noahg460505/Needlessly-Overcomplicated-Widget-Sorter/Diagrams/12_5-Fritzing.png

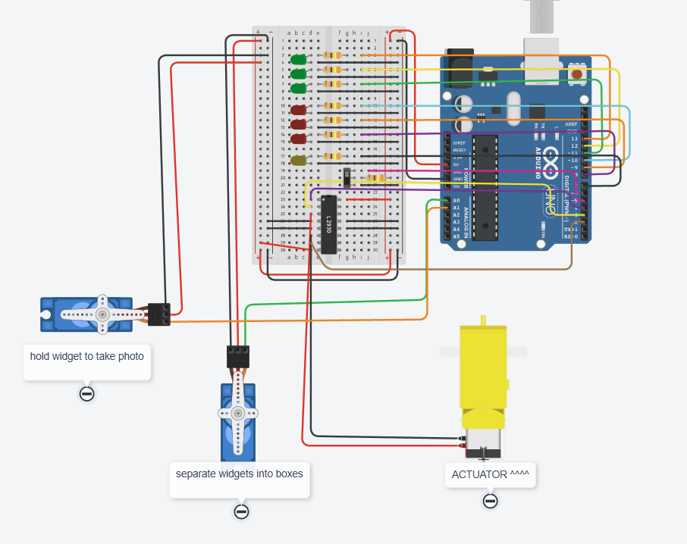
Diagrams/12_5-Fritzing.png
