noahg460505/Needlessly-Overcomplicated-Widget-Sorter/photos-videos/actuator_1.jpg

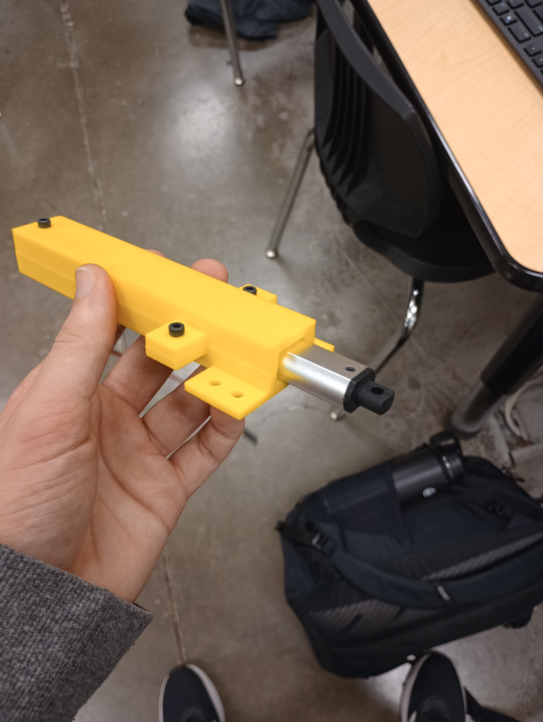
photos-videos/actuator_1.jpg
