noahg460505/Needlessly-Overcomplicated-Widget-Sorter/photos-videos/actuator_2.jpg

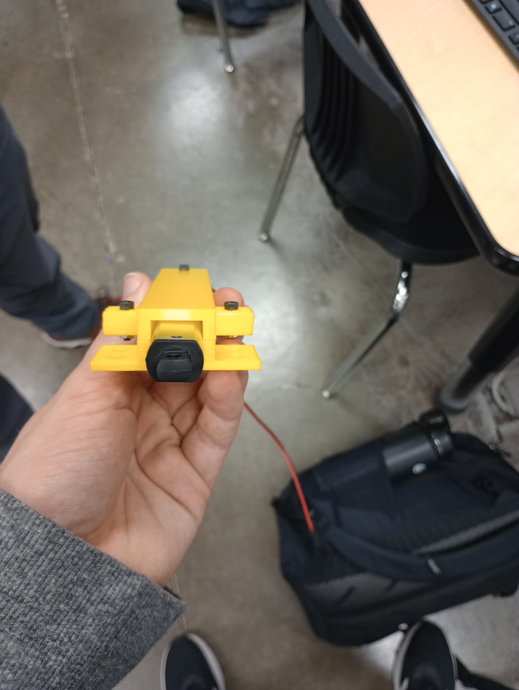
photos-videos/actuator_2.jpg
