noahg460505/Needlessly-Overcomplicated-Widget-Sorter/photos-videos/capture_zone.jpg

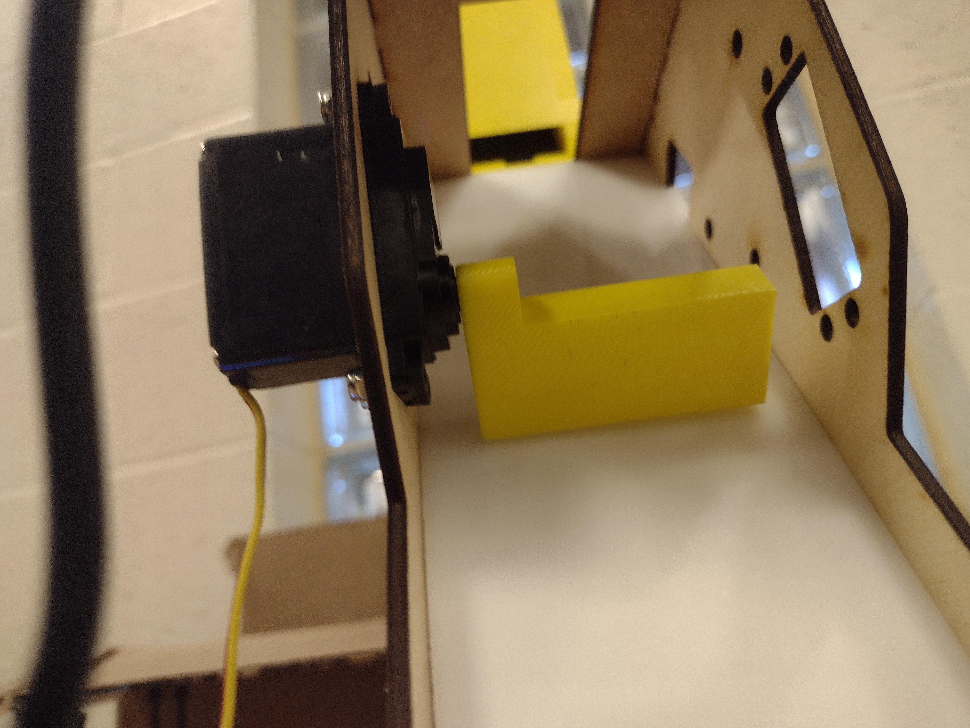
photos-videos/capture_zone.jpg
