noahg460505/Needlessly-Overcomplicated-Widget-Sorter/photos-videos/markus_doing_cad.jpg

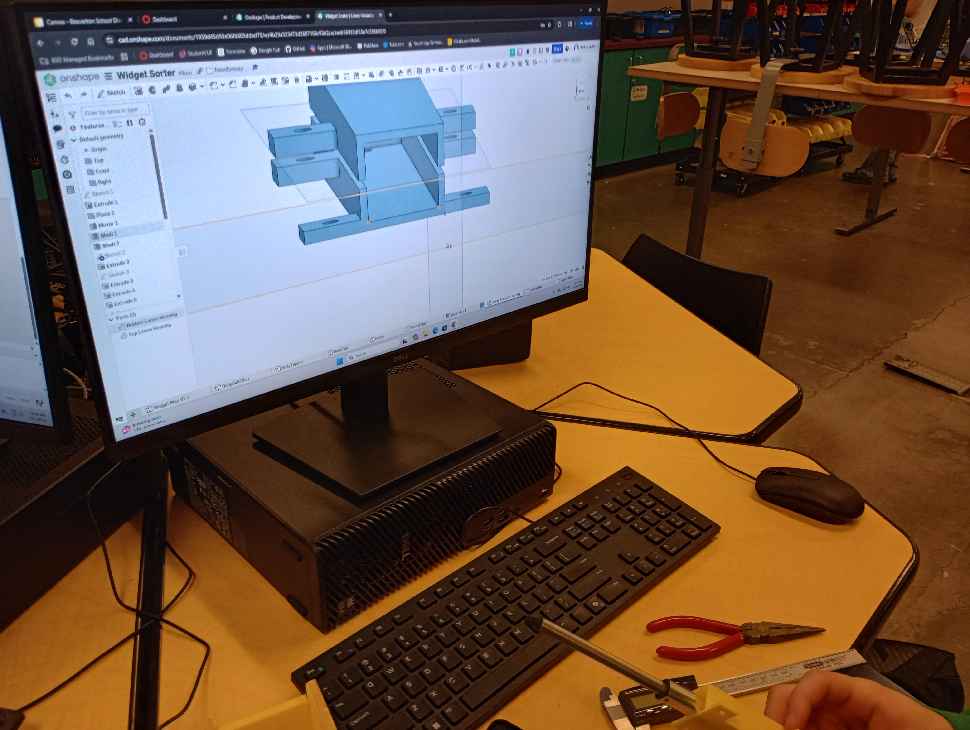
photos-videos/markus_doing_cad.jpg
