noahg460505/Needlessly-Overcomplicated-Widget-Sorter/photos-videos/markus_with_actuator.jpg

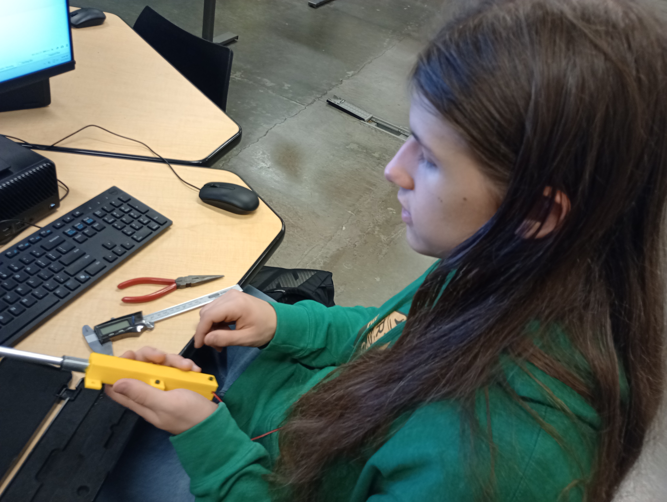
photos-videos/markus_with_actuator.jpg
