noahg460505/Needlessly-Overcomplicated-Widget-Sorter/photos-videos/noah.jpg

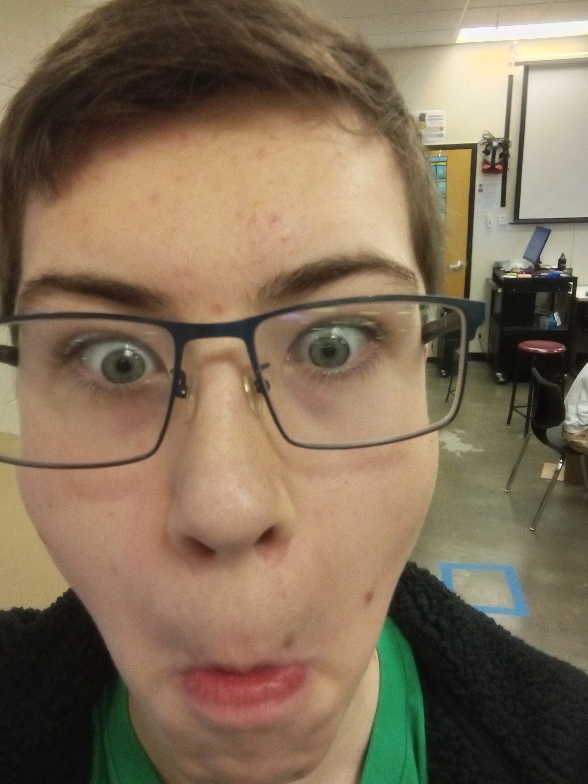
photos-videos/noah.jpg
