noahg460505/Needlessly-Overcomplicated-Widget-Sorter/photos-videos/servo_motor.jpg

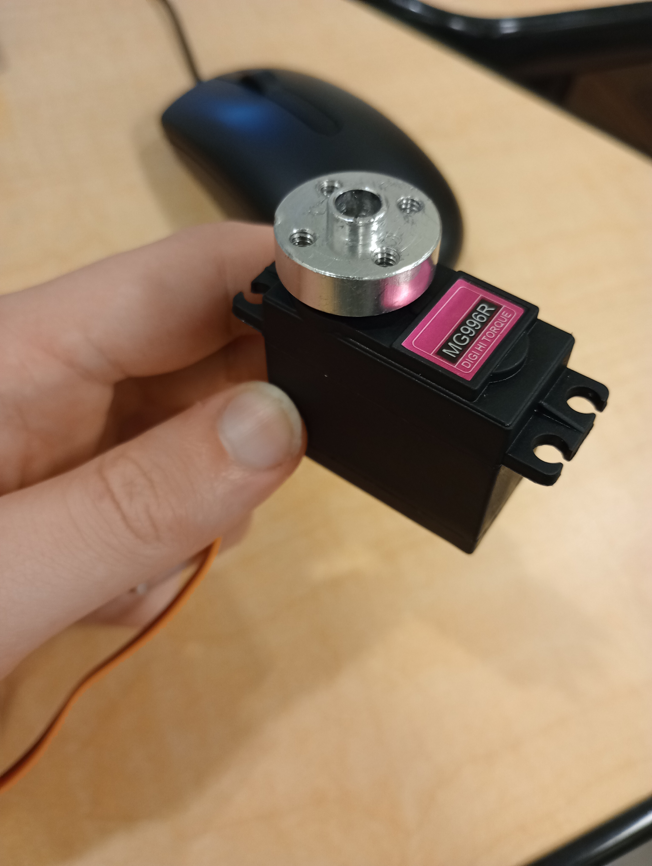
photos-videos/servo_motor.jpg
