noahg460505/Needlessly-Overcomplicated-Widget-Sorter/photos-videos/widget_mag_1.jpg

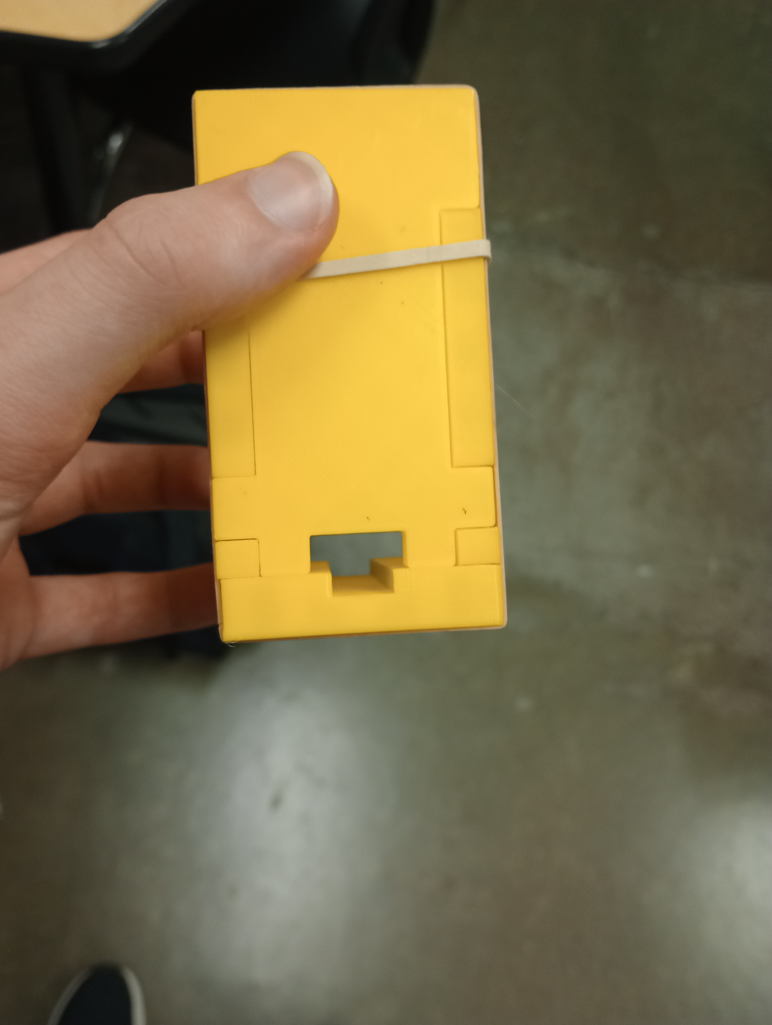
photos-videos/widget_mag_1.jpg
