noahg460505/Needlessly-Overcomplicated-Widget-Sorter/photos-videos/yarema.jpg

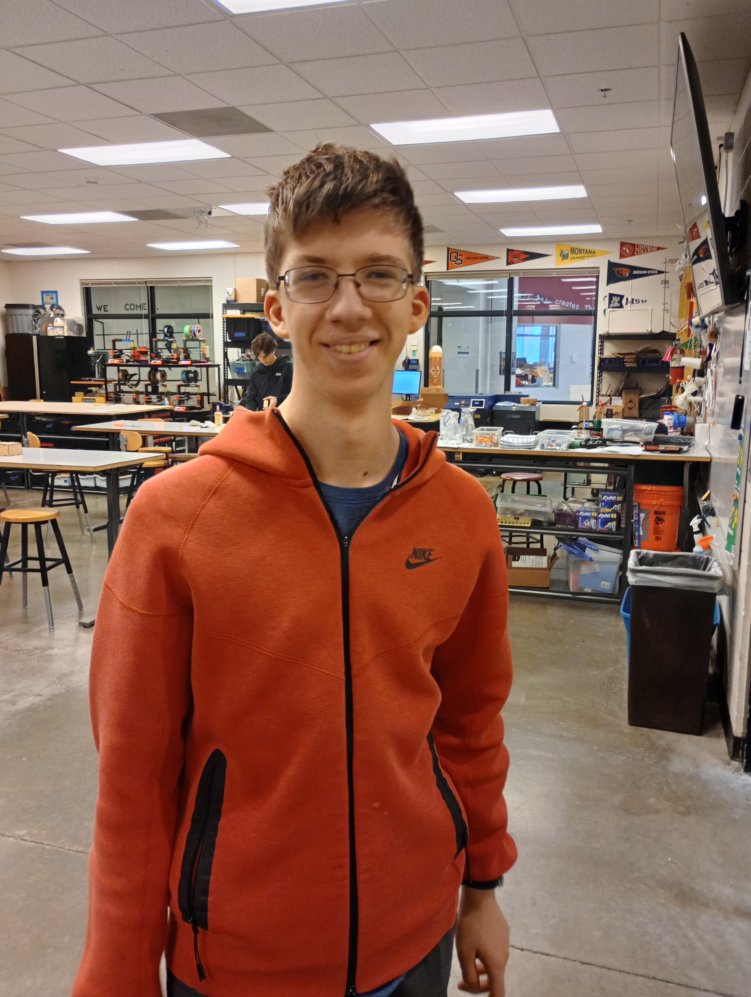
photos-videos/yarema.jpg
