noahg460505/Needlessly-Overcomplicated-Widget-Sorter/CAD/laser-files/flipper-flopper.dxf

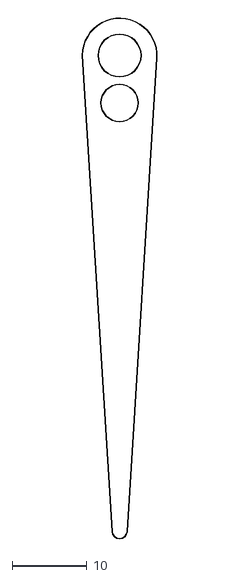
[picture p45: CAD file, 2026-01-20]
CAD/laser-files/flipper-flopper.dxf
10.1 x 70.1
