noahg460505/Needlessly-Overcomplicated-Widget-Sorter/Diagrams/12_1-Wiring.png

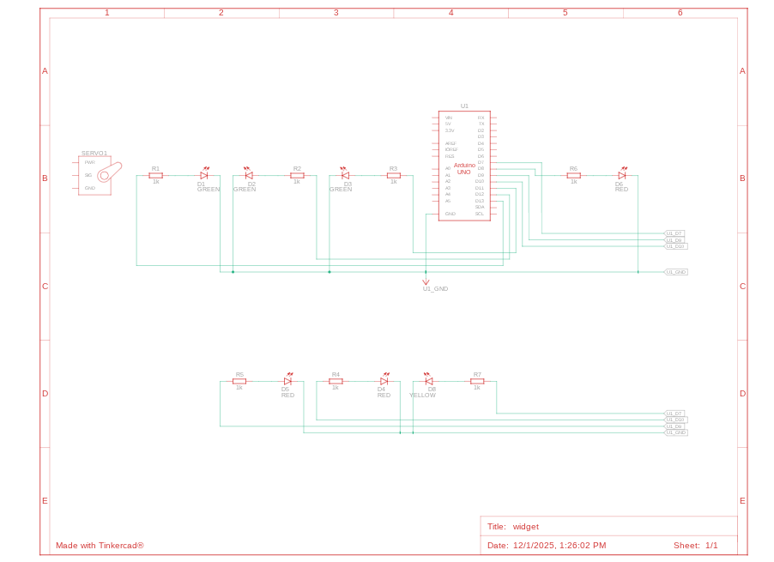
Diagrams/12_1-Wiring.png
