noahg460505/Needlessly-Overcomplicated-Widget-Sorter/Diagrams/12_3 - Wiring.png

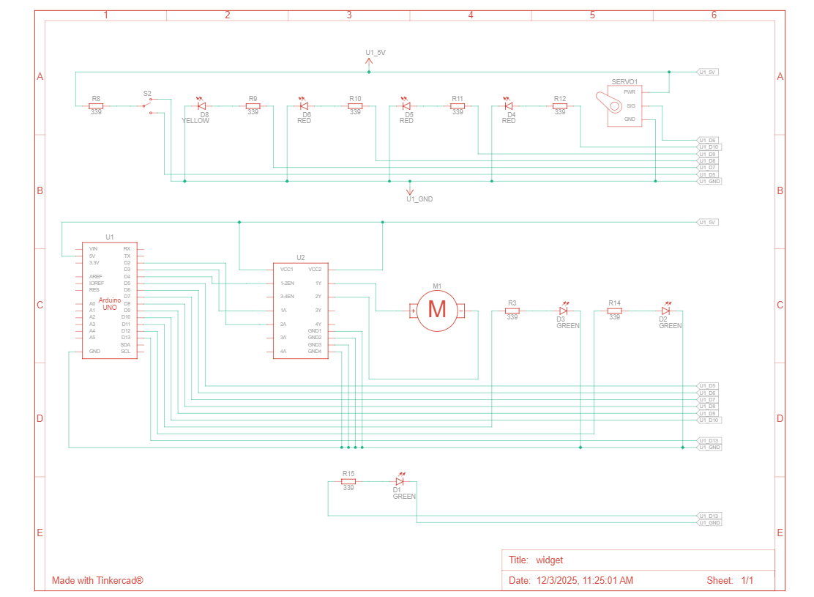
Diagrams/12_3 - Wiring.png
