noahg460505/Needlessly-Overcomplicated-Widget-Sorter/photos-videos/sorter_top.jpg

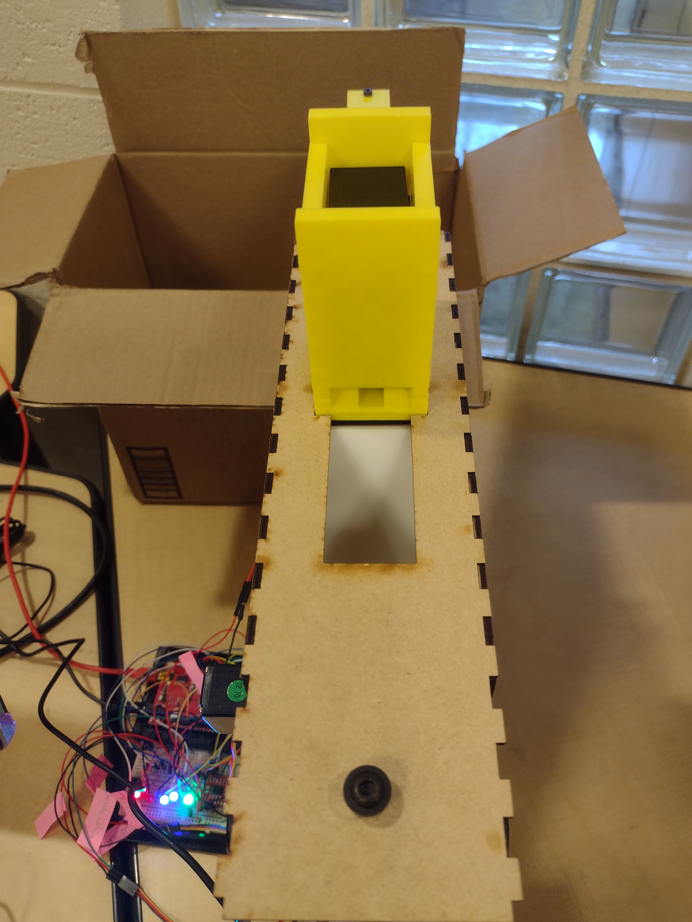
photos-videos/sorter_top.jpg
